kuato781/spektrum-ix14-stand/v2/documentation/product-images/04-v2_extended_side.jpg

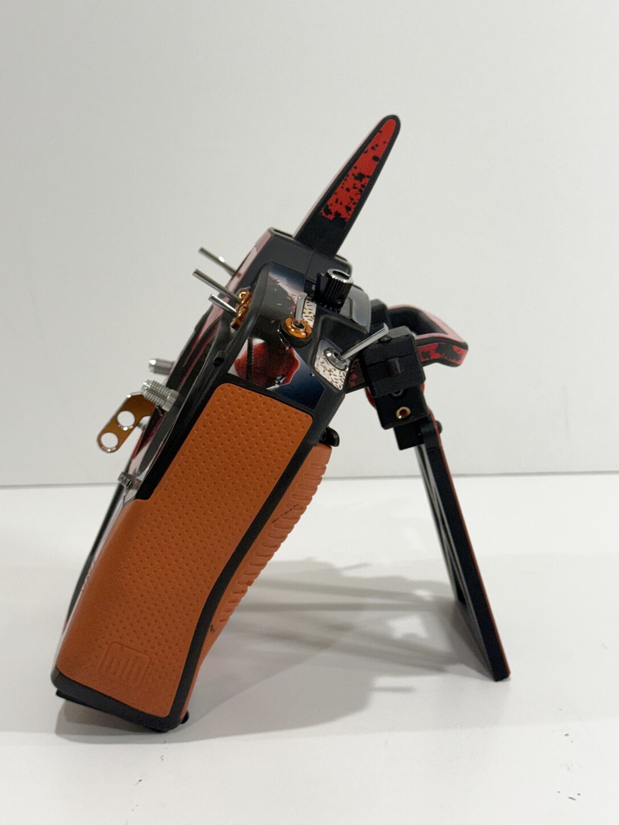
v2/documentation/product-images/04-v2_extended_side.jpg
