kuato781/spektrum-ix14-stand/v2/documentation/product-images/05-v2_extended.jpg

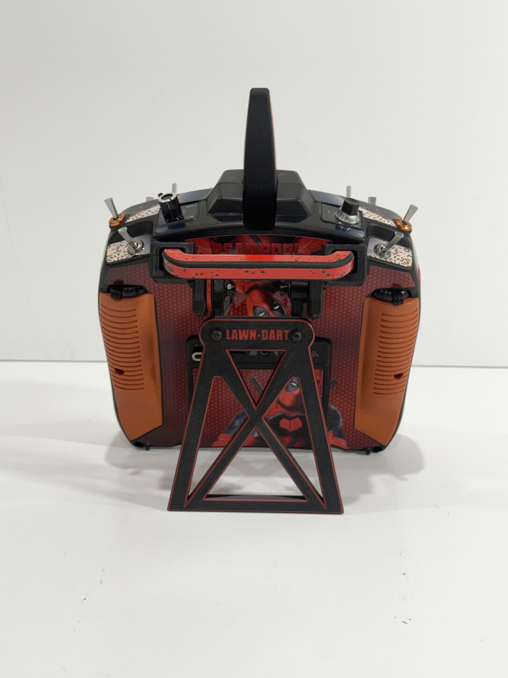
v2/documentation/product-images/05-v2_extended.jpg
