kuato781/spektrum-ix14-stand/v2/documentation/product-images/07-v2_extended_side_max.jpg

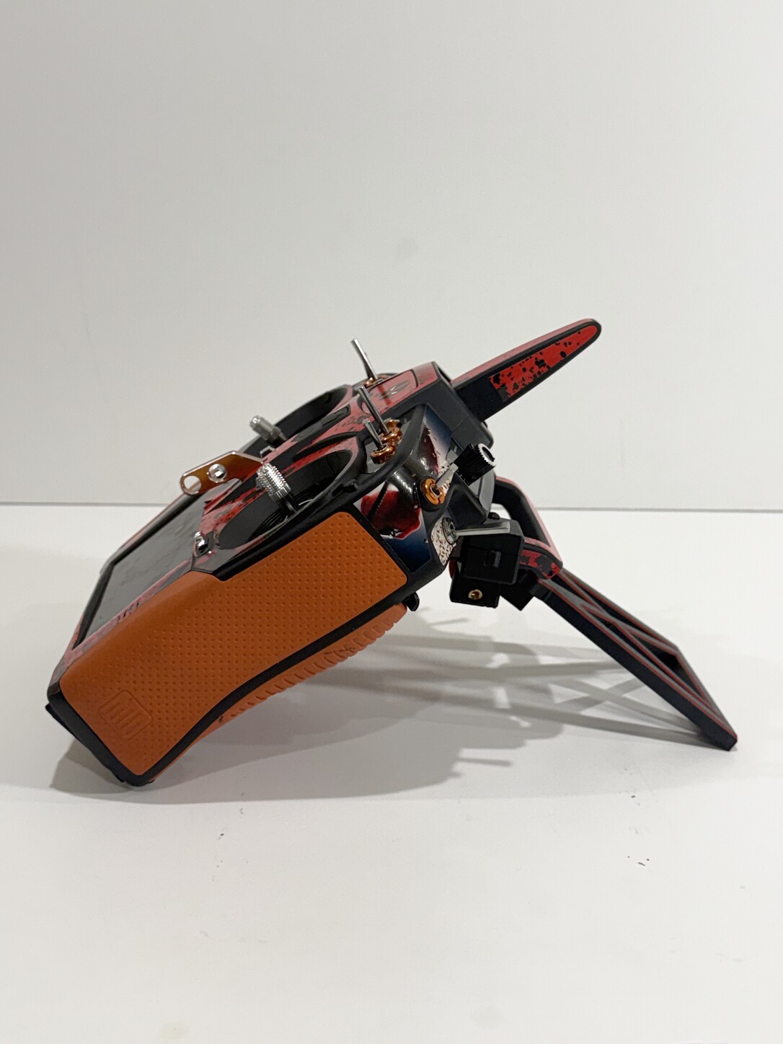
v2/documentation/product-images/07-v2_extended_side_max.jpg
