kuato781/spektrum-ix14-stand/v2/documentation/product-images/01-v2_components.jpg

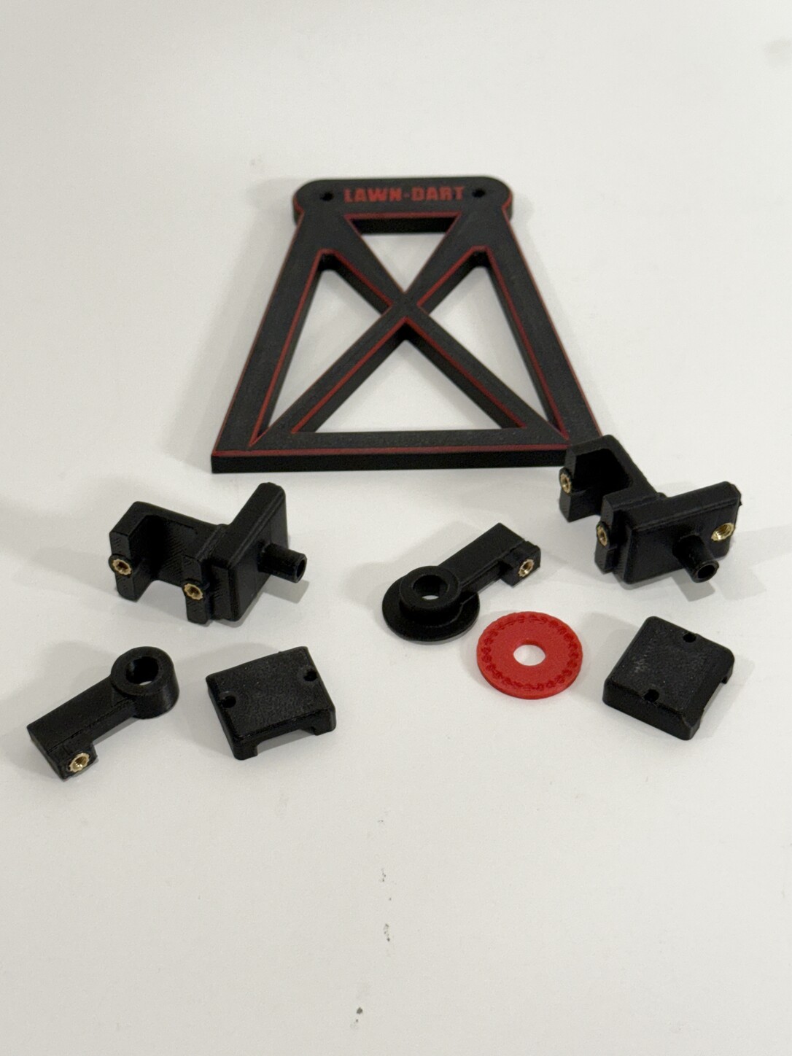
v2/documentation/product-images/01-v2_components.jpg
