kuato781/spektrum-ix14-stand/v2/documentation/product-images/02-v2_assembled.jpg

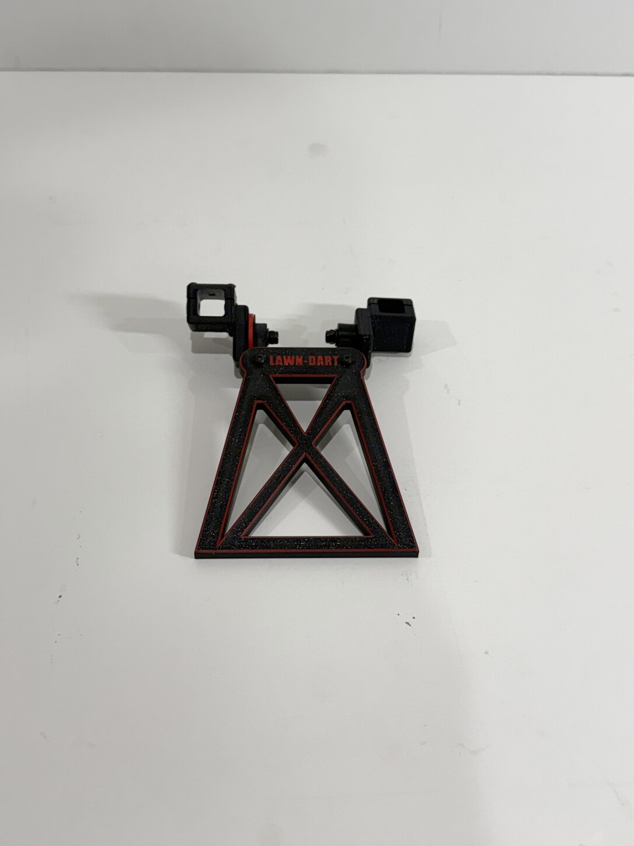
v2/documentation/product-images/02-v2_assembled.jpg
